picli3/e-tracker/screenshots/e-track-B_Cu.png

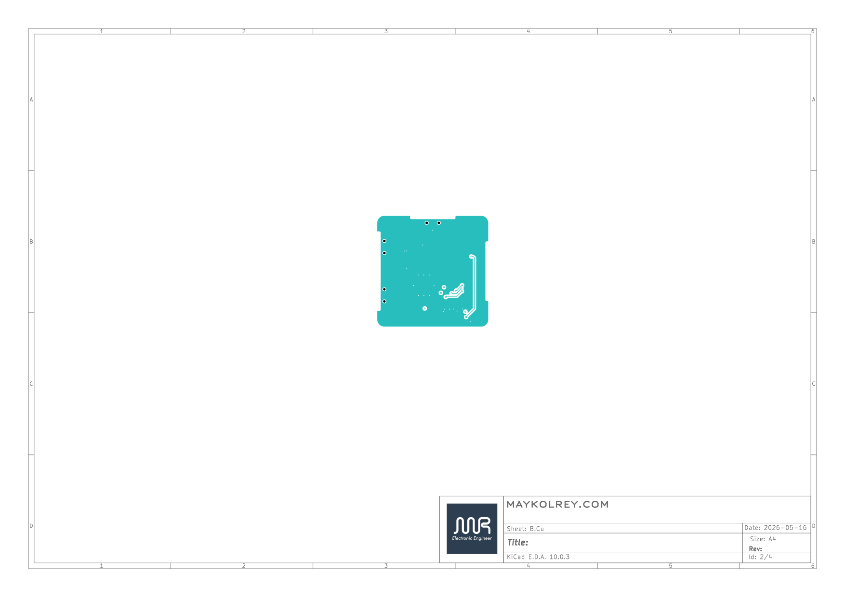
screenshots/e-track-B_Cu.png
